DanielHeEGG/OpenTEC/Firmware/include/adc.h

/**
  ******************************************************************************
  * @file    adc.h
  * @brief   Header for adc.c file.
  ******************************************************************************
  */

#include "main.h"

extern ADC_HandleTypeDef hadc1;

void MX_ADC1_Init(void);
