DanielHeEGG/OpenTEC/Firmware/include/gpio.h

/**
  ******************************************************************************
  * @file    gpio.h
  * @brief   Header for gpio.c file.
  ******************************************************************************
  */

#include "main.h"

void MX_GPIO_Init(void);
