DanielHeEGG/OpenTEC/Firmware/include/i2c.h

/**
  ******************************************************************************
  * @file    i2c.h
  * @brief   Header for i2c.c file.
  ******************************************************************************
  */

#include "main.h"

extern I2C_HandleTypeDef hi2c2;

void MX_I2C2_Init(void);
