DanielHeEGG/OpenTEC/Firmware/include/tim.h

/**
  ******************************************************************************
  * @file    tim.h
  * @brief   This file contains all the function prototypes for
  *          the tim.c file
  ******************************************************************************
  */

#include "main.h"

extern TIM_HandleTypeDef htim3;
extern TIM_HandleTypeDef htim4;

void MX_TIM3_Init(void);
void MX_TIM4_Init(void);
void HAL_TIM_MspPostInit(TIM_HandleTypeDef *htim);
