DanielHeEGG/OpenTEC/Firmware/src/gpio.c

/**
  ******************************************************************************
  * @file    gpio.c
  * @brief   GPIO configurations.
  ******************************************************************************
  */

#include "gpio.h"

/**
  * @brief  Initialize GPIO.
  * @retval None
  */
void MX_GPIO_Init(void) {
    __HAL_RCC_GPIOD_CLK_ENABLE();
    __HAL_RCC_GPIOA_CLK_ENABLE();
    __HAL_RCC_GPIOB_CLK_ENABLE();

    GPIO_InitTypeDef GPIO_InitStruct;

    GPIO_InitStruct.Pin = LCD_D4_Pin | LCD_D5_Pin | LCD_D6_Pin | LCD_D7_Pin | STATUS_LED_Pin;
    GPIO_InitStruct.Mode = GPIO_MODE_OUTPUT_PP;
    GPIO_InitStruct.Pull = GPIO_NOPULL;
    GPIO_InitStruct.Speed = GPIO_SPEED_FREQ_LOW;
    HAL_GPIO_Init(GPIOA, &GPIO_InitStruct);

    GPIO_InitStruct.Pin = LCD_RS_Pin | LCD_EN_Pin | HB1_SD_Pin | HB2_SD_Pin;
    GPIO_InitStruct.Mode = GPIO_MODE_OUTPUT_PP;
    GPIO_InitStruct.Pull = GPIO_NOPULL;
    GPIO_InitStruct.Speed = GPIO_SPEED_FREQ_LOW;
    HAL_GPIO_Init(GPIOB, &GPIO_InitStruct);

    GPIO_InitStruct.Pin = SW_L_Pin | SW_M_Pin | SW_R_Pin;
    GPIO_InitStruct.Mode = GPIO_MODE_IT_RISING;
    GPIO_InitStruct.Pull = GPIO_NOPULL;
    HAL_GPIO_Init(GPIOB, &GPIO_InitStruct);

    HAL_NVIC_SetPriority(EXTI15_10_IRQn, 5, 0);
    HAL_NVIC_EnableIRQ(EXTI15_10_IRQn);
}
